ALittleSlow/Ultimate-Drawer-System/examples/insert 59x118x17, 0.10 tolerance for 1x1 drawer.stl

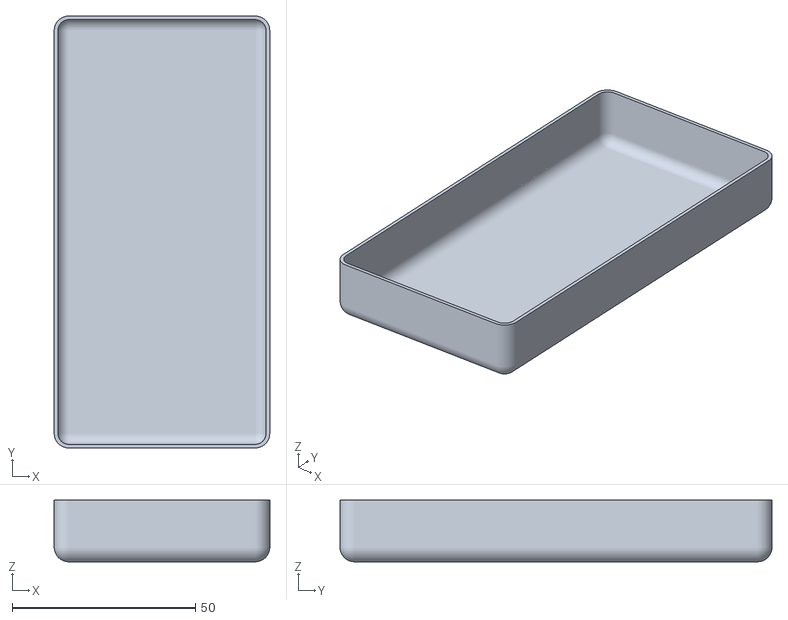
[picture p15: CAD file, 2019-10-12]
examples/insert 59x118x17, 0.10 tolerance for 1x1 drawer.stl
58.8 x 117.8 x 16.8
