ALittleSlow/Ultimate-Drawer-System/examples/insert 59x59x10 for 1x1 drawer.stl

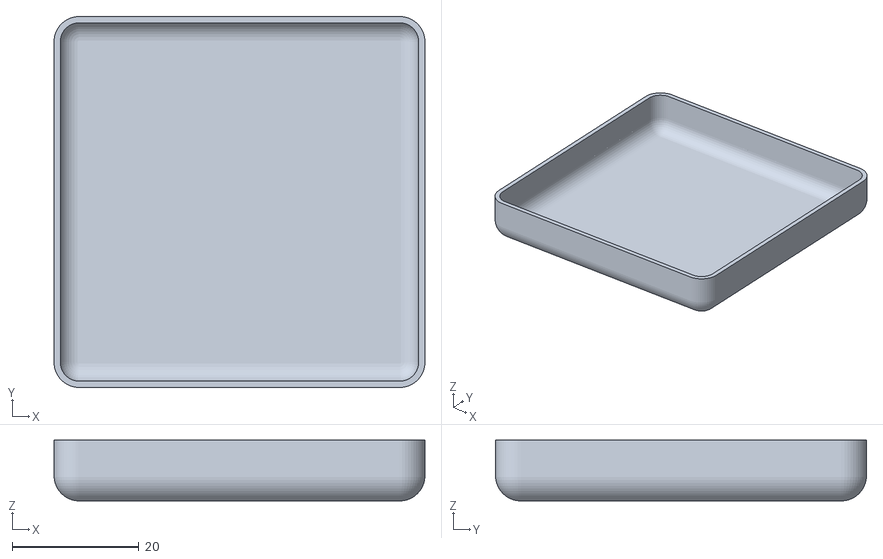
[picture p16: CAD file, 2019-10-12]
examples/insert 59x59x10 for 1x1 drawer.stl
58.6 x 58.6 x 9.60
