ALittleSlow/Ultimate-Drawer-System/examples/insert 118x118x10 round island 45-20 for 1x1 drawer.stl

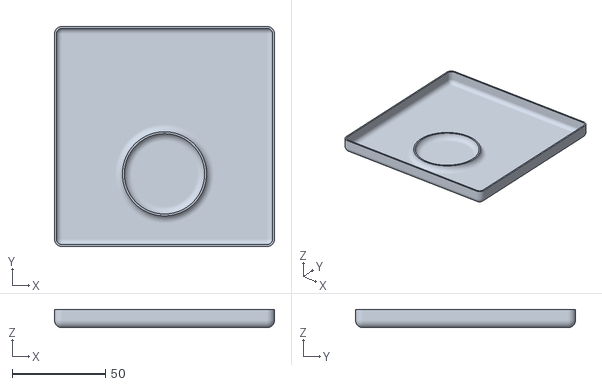
[picture p17: CAD file, 2019-10-12]
examples/insert 118x118x10 round island 45-20 for 1x1 drawer.stl
117.8 x 117.8 x 9.80
