ALittleSlow/Ultimate-Drawer-System/examples/insert 82x182x10 plier45x15+30 for 1D drawer.stl

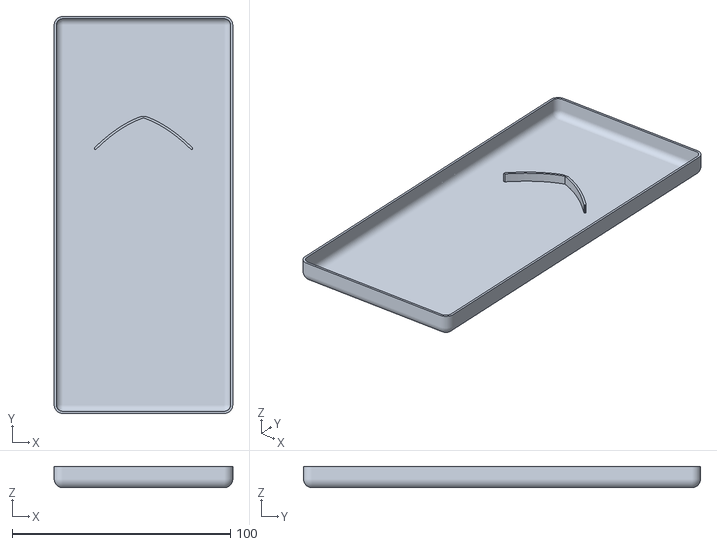
[picture p18: CAD file, 2019-10-12]
examples/insert 82x182x10 plier45x15+30 for 1D drawer.stl
81.8 x 181.8 x 9.80
