ALittleSlow/Ultimate-Drawer-System/examples/insert 39.3x39.3x10, 0.10 tolerance for 1x1 drawer.stl

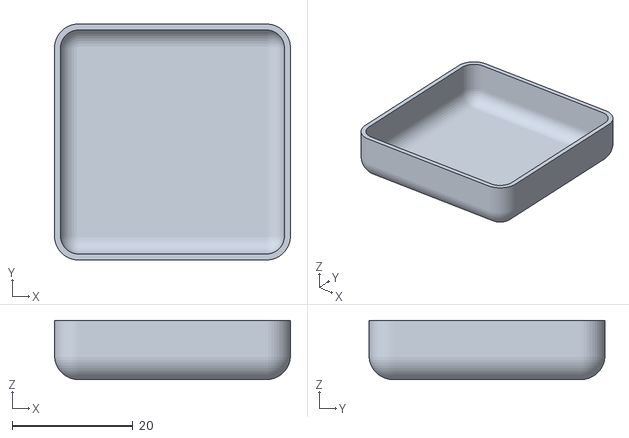
[picture p19: CAD file, 2019-10-12]
examples/insert 39.3x39.3x10, 0.10 tolerance for 1x1 drawer.stl
39.1 x 39.1 x 9.80
