ALittleSlow/Ultimate-Drawer-System/examples/drawer 1U ergo catch lock noLabel.stl

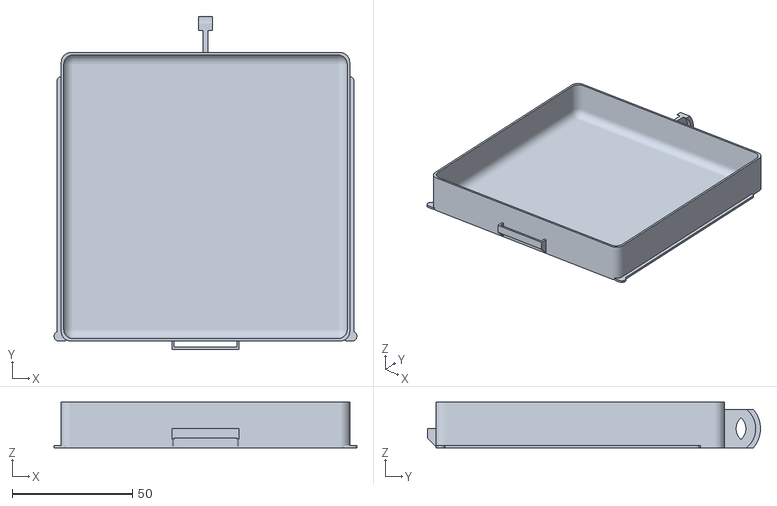
[picture p20: CAD file, 2019-10-12]
examples/drawer 1U ergo catch lock noLabel.stl
126.0 x 138.5 x 19.0
