ALittleSlow/Ultimate-Drawer-System/examples/lock 2U.stl

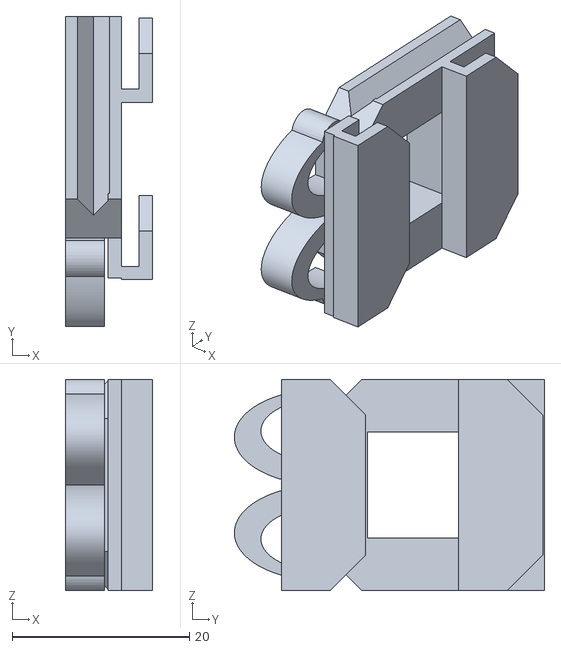
[picture p21: CAD file, 2019-10-12]
examples/lock 2U.stl
9.81 x 35.0 x 23.8
