ALittleSlow/Ultimate-Drawer-System/examples/drawer 0.5Wx05.Dx1H ergo catch noLock.stl

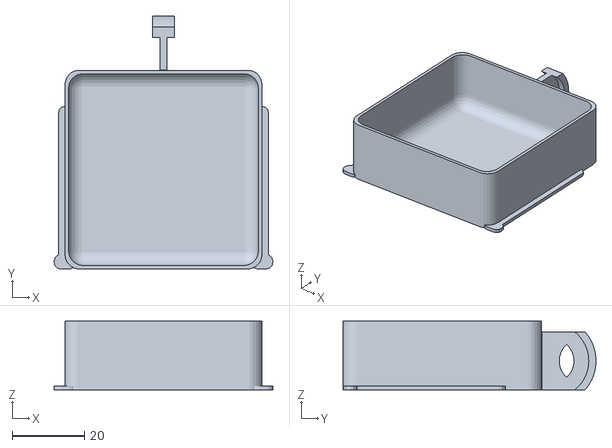
[picture p22: CAD file, 2019-10-12]
examples/drawer 0.5Wx05.Dx1H ergo catch noLock.stl
60.5 x 70.0 x 19.0
