ALittleSlow/Ultimate-Drawer-System/examples/shelf 0.5Wx0.5Dx2H noHoles clip rearWeak frontStrong.stl

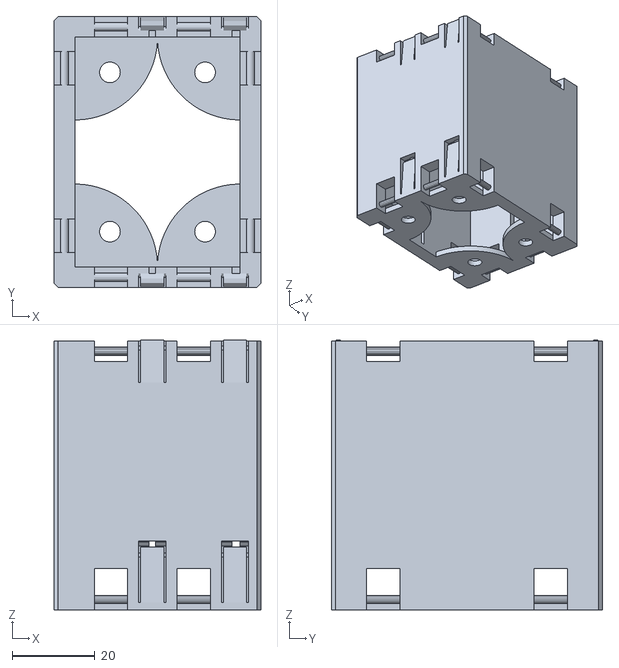
[picture p23: CAD file, 2019-10-12]
examples/shelf 0.5Wx0.5Dx2H noHoles clip rearWeak frontStrong.stl
50.0 x 65.5 x 65.2
