ALittleSlow/Ultimate-Drawer-System/examples/insert 29.5x29.5x10 for 1x1 drawer.stl

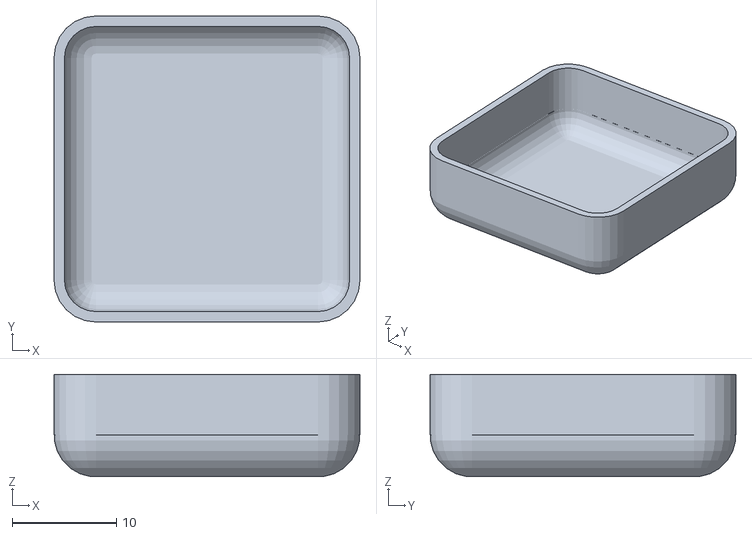
[picture p24: CAD file, 2019-10-12]
examples/insert 29.5x29.5x10 for 1x1 drawer.stl
29.3 x 29.3 x 9.77
