ALittleSlow/Ultimate-Drawer-System/examples/shelf 1Wx1Dx2U clip lock rearMedium frontMedium.stl

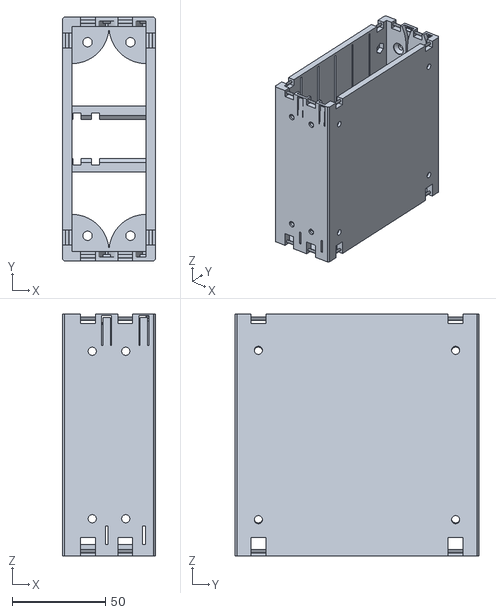
[picture p25: CAD file, 2019-10-12]
examples/shelf 1Wx1Dx2U clip lock rearMedium frontMedium.stl
50.0 x 131.0 x 130.0
