ALittleSlow/Ultimate-Drawer-System/examples/drawer 1U ergo catch lock.stl

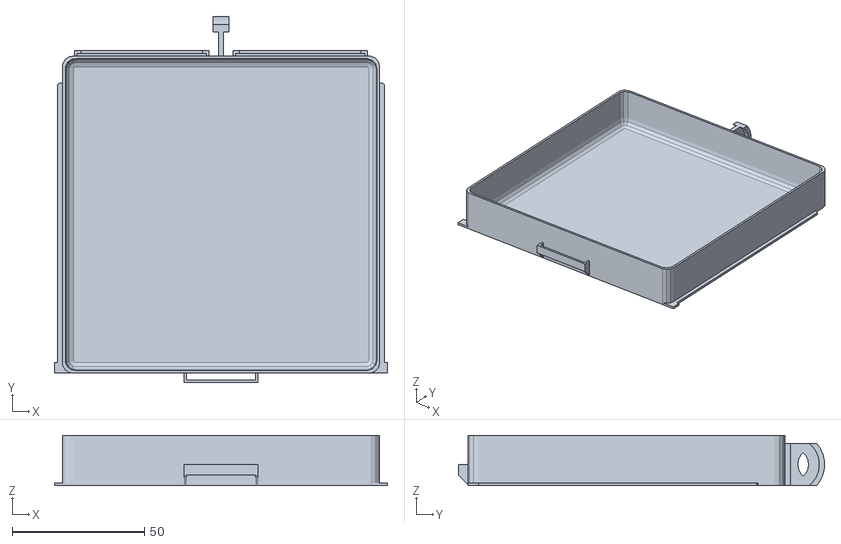
[picture p26: CAD file, 2019-10-12]
examples/drawer 1U ergo catch lock.stl
126.0 x 138.4 x 19.0
