ALittleSlow/Ultimate-Drawer-System/examples/drawer 1U noFlange noLabel.stl

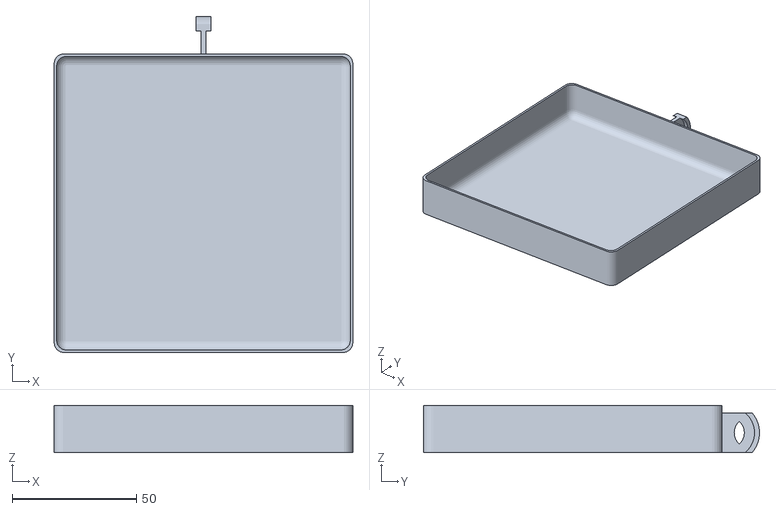
[picture p27: CAD file, 2019-10-12]
examples/drawer 1U noFlange noLabel.stl
120.0 x 135.0 x 19.0
