ALittleSlow/Ultimate-Drawer-System/examples/clip 0.3 tolerance.stl

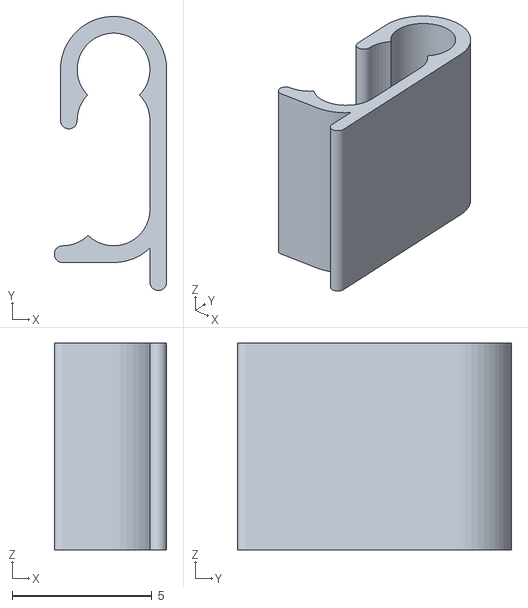
[picture p28: CAD file, 2019-10-12]
examples/clip 0.3 tolerance.stl
4.02 x 9.80 x 7.40
