ALittleSlow/Ultimate-Drawer-System/examples/foot v1.1.stl

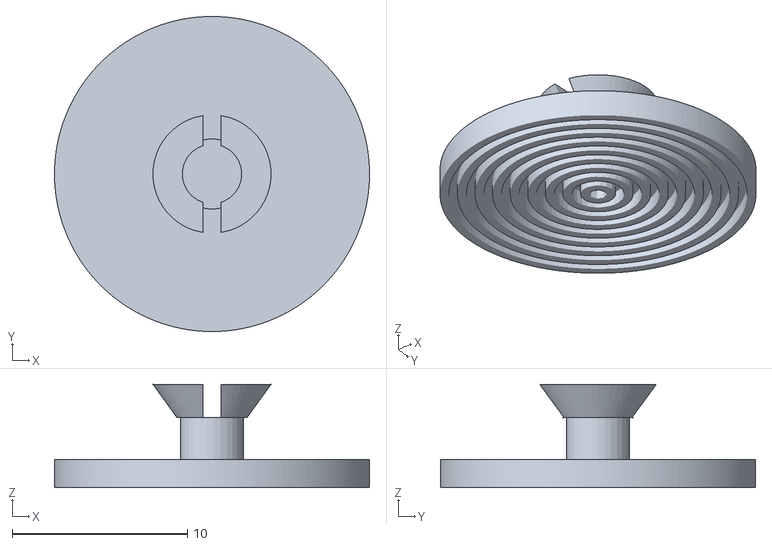
[picture p29: CAD file, 2019-10-12]
examples/foot v1.1.stl
18.0 x 18.0 x 5.91
