ALittleSlow/Ultimate-Drawer-System/examples/shelf Becky's Jewelry Box shelf 2x1x5.stl

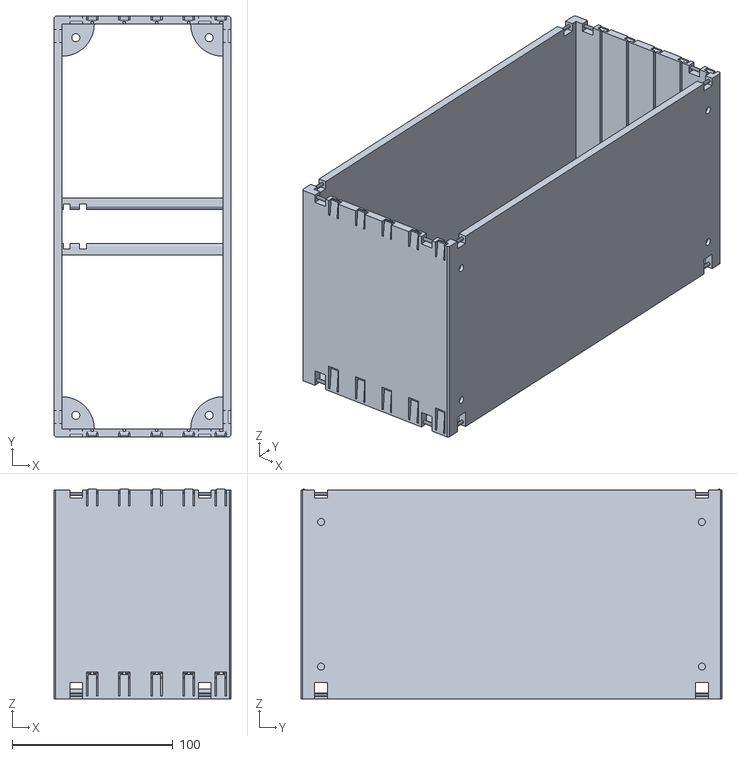
[picture p30: CAD file, 2019-10-12]
examples/shelf Becky's Jewelry Box shelf 2x1x5.stl
110.0 x 262.0 x 130.4
