ALittleSlow/Ultimate-Drawer-System/examples/shelf Becky's Jewelry Box 1x1x10.stl

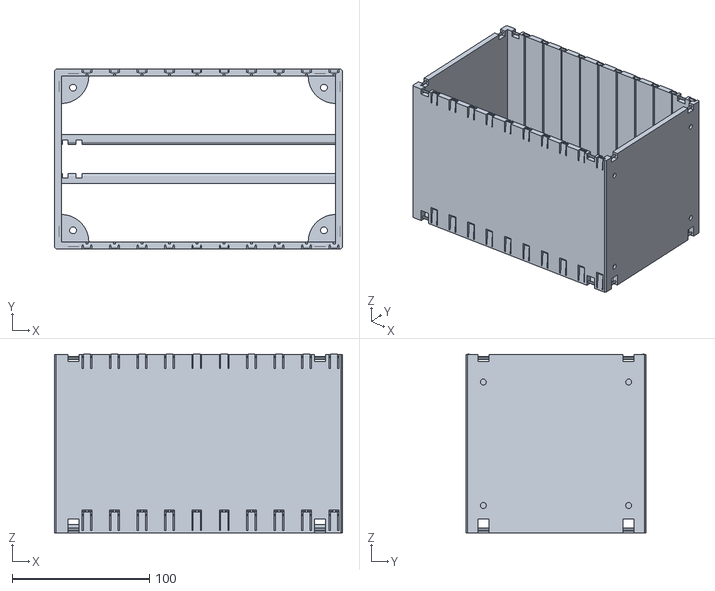
[picture p31: CAD file, 2019-10-12]
examples/shelf Becky's Jewelry Box 1x1x10.stl
210.0 x 131.0 x 130.4
