ALittleSlow/Ultimate-Drawer-System/examples/shelf Brians 3D Printer Toolbox.stl

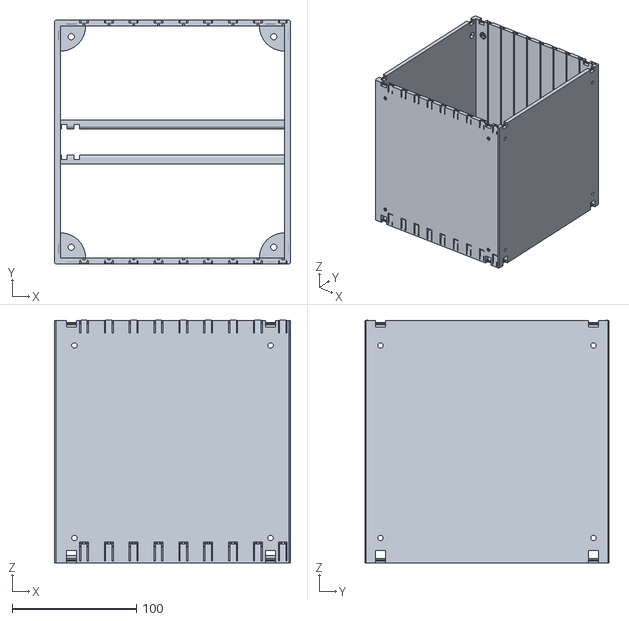
[picture p32: CAD file, 2019-10-12]
examples/shelf Brians 3D Printer Toolbox.stl
190.0 x 196.5 x 195.4
