ALittleSlow/Ultimate-Drawer-System/examples/insert 56.5x182x10 for 1x1 drawer.stl

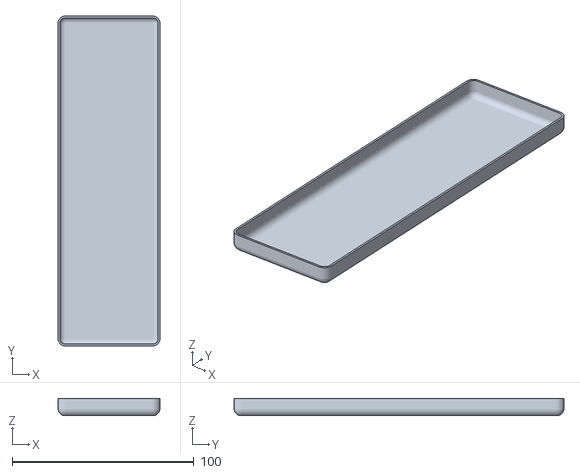
[picture p33: CAD file, 2019-08-11]
examples/insert 56.5x182x10 for 1x1 drawer.stl
56.1 x 181.6 x 9.57
