ALittleSlow/Ultimate-Drawer-System/examples/drawer 1U ergo.stl

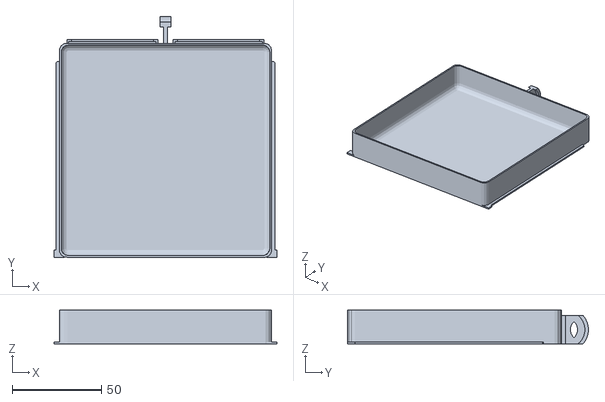
[picture p34: CAD file, 2019-08-09]
examples/drawer 1U ergo.stl
125.0 x 134.9 x 19.0
